Onwrikbaar/NeoDK/Enclosure/blue.png

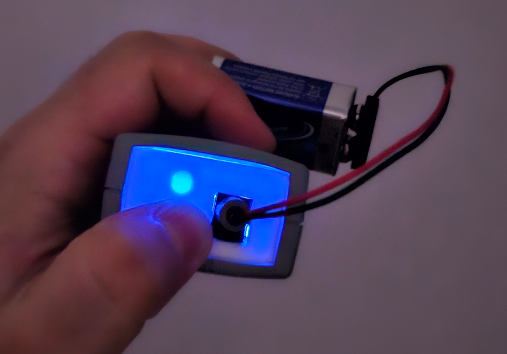
Enclosure/blue.png
