Onwrikbaar/NeoDK/pictures/enclosure.png

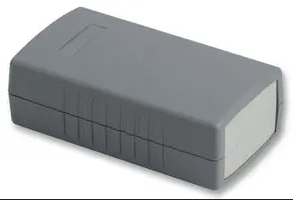
pictures/enclosure.png
