Onwrikbaar/NeoDK/firmware/neodk/src/debug_cli.c

/*
 * debug_cli.c
 *
 *  NOTICE (do not remove):
 *      This file is part of project NeoDK (https://github.com/Onwrikbaar/NeoDK).
 *      See https://github.com/Onwrikbaar/NeoDK/blob/main/LICENSE.txt for full license details.
 *
 *  Created on: 26 Mar 2024
 *      Author: mark
 *   Copyright  2024, 2025 Neostim™
 */

#include <stdio.h>

#include "bsp_dbg.h"
#include "bsp_mao.h"
#include "bsp_app.h"
#include "app_event.h"

// This module implements:
#include "debug_cli.h"


typedef struct {
    uint8_t buf[20];
    EventQueue *delegate;
    Sequencer *sequencer;
    DataLink *datalink;
    uint8_t state;
    uint8_t len;
} CmndInterp;

static CmndInterp my = {0};


static void gatherInputCharacters(CmndInterp *me, char ch)
{
    me->buf[me->len] = '\0';
    if (ch == '\n' || (me->buf[me->len++] = ch, me->len == sizeof me->buf)) {
        if (ch != '\n') BSP_logf("\n");         // Buffer is full, no newline seen.
        BSP_logf("Console: '%s'\n", me->buf);
        me->len = 0;
    }
}


static void setIntensity(CmndInterp *me, uint8_t intensity_perc)
{
    EventQueue_postEvent((EventQueue *)me->sequencer, ET_SET_INTENSITY, &intensity_perc, sizeof intensity_perc);
}


static void changeIntensity(CmndInterp *me, int8_t delta_perc)
{
    int16_t soll_perc = (int16_t)Sequencer_getIntensityPercentage(me->sequencer) + delta_perc;
    if (soll_perc < 10) soll_perc = 10;
    else if (soll_perc > 100) soll_perc = 100;
    setIntensity(me, soll_perc);
}

/**
 * @brief   Console commands for interactive testing.
 */
static void interpretCommand(CmndInterp *me, char ch)
{
    switch (ch)
    {
        case '?':
            CLI_logf("Commands: /? /a /b /d /l /n /q /s /u /v /w /0 /1../9\n");
            break;
        case '0':
            BSP_primaryVoltageEnable(false);
            setIntensity(me, 0);
            break;
        case '1': case '2': case '3': case '4': case '5': case '6': case '7': case '8': case '9':
            setIntensity(me, (ch - '0') * 10);  // 0..90%.
            BSP_primaryVoltageEnable(true);     // Turn on the buck converter.
            break;
        case 'a':
            BSP_triggerADC();
            break;
        case 'b':                               // Simulate a button press.
            EventQueue_postEvent(me->delegate, ET_BUTTON_PUSHED, NULL, 0);
            EventQueue_postEvent(me->delegate, ET_BUTTON_RELEASED, NULL, 0);
            break;
        case 'd':                               // Intensity down.
            changeIntensity(me, -2);
            break;
        case 'l':
            BSP_toggleTheLED();
            break;
        case 'n':
            EventQueue_postEvent((EventQueue *)me->sequencer, ET_SELECT_NEXT_PATTERN, NULL, 0);
            break;
        case 'q': {                             // Quit.
            int sig = 2;                        // Simulate Ctrl-C.
            EventQueue_postEvent(me->delegate, ET_POSIX_SIGNAL, (uint8_t const *)&sig, sizeof sig);
            break;
        }
        case 's':
            EventQueue_postEvent((EventQueue *)me->sequencer, ET_STOP, NULL, 0);
            break;
        case 'u':                               // Intensity up.
            changeIntensity(me, +2);
            break;
        case 'v':
            CLI_logf("Firmware %s\n", BSP_firmwareVersion());
            break;
        case 'w':                               // Allow rediscovery by Dweeb.
            CLI_logf("Accept connection from Dweeb\n");
            DataLink_awaitSync(me->datalink);
            break;
        default:
            CLI_logf("Unknown command '/%c'\n", ch);
    }
}


static void handleConsoleInput(CmndInterp *me, char ch)
{
    if (me->state == 0) {
        if (ch == '/') me->state = 1;
        else gatherInputCharacters(me, ch);
    } else {                                    // '/' seen.
        if (ch == '\n') {                       // Not a command.
            gatherInputCharacters(me, '/');
            gatherInputCharacters(me, ch);
        } else {
            BSP_logf("\n");
            interpretCommand(me, ch);
        }
        me->state = 0;
    }
}


static void vLogToUser(CmndInterp *me, char const *fmt, va_list args)
{
    char msg[80];
    int nbw = vsnprintf(msg, sizeof msg, fmt, args);
    if (nbw > 0) DataLink_sendDebugPacket(me->datalink, (uint8_t const *)msg, nbw + 1);
}

/*
 * Below are the functions implementing this module's interface.
 */

void CLI_init(EventQueue *dq, Sequencer *sequencer, DataLink *datalink)
{
    my.delegate = dq;
    my.sequencer = sequencer;
    my.datalink = datalink;
}


int CLI_logf(char const *fmt, ...)
{
    va_list args;
    va_start(args, fmt);
    int nbw = BSP_vlogf(fmt, args);
    vLogToUser(&my, fmt, args);
    va_end(args);
    return nbw;
}


void CLI_handleRemoteInput(uint8_t const *cmnd, uint16_t len)
{
    if (len == 2 && cmnd[0] == '/') {
        interpretCommand(&my, cmnd[1]);
    } else {
        char response[len + 5];
        int nc = snprintf(response, sizeof response, "'%.*s'?\n", len, cmnd);
        if (nc > 0 && nc < sizeof response) {
            DataLink_sendDebugPacket(my.datalink, (uint8_t const *)response, nc);
        }
    }
}


void BSP_idle(bool (*maySleep)(void const *), void const *context)
{
    char ch;
    if (BSP_readConsole(&ch, 1)) {
        handleConsoleInput(&my, ch);
    }

    if (maySleep != NULL) {
        BSP_criticalSectionEnter();
        if (maySleep(context)) {
            // All pending events have been handled.
            BSP_sleepMCU();
        }
        BSP_criticalSectionExit();
    }
}
