Onwrikbaar/NeoDK/firmware/neodk/src/pattern_iter.c

/*
 * pattern_iter.c
 *
 *  NOTICE (do not remove):
 *      This file is part of project NeoDK (https://github.com/Onwrikbaar/NeoDK).
 *      See https://github.com/Onwrikbaar/NeoDK/blob/main/LICENSE.txt for full license details.
 *
 *  Created on: 6 Mar 2024
 *      Author: mark
 *   Copyright  2024, 2025 Neostim™
 */

#include "bsp_dbg.h"

// This module implements:
#include "pattern_iter.h"


static void nextElconIfLastStep(PatternIterator *me)
{
    PatternDescr const *pd = me->pattern_descr;
    if (me->step_nr == pd->nr_of_steps - 1) {   // Transition done.
        me->step_nr = 0;
        if (++me->elcon_nr == pd->nr_of_elcons) {
            me->elcon_nr = 0;                   // Wrap around.
            me->nr_of_reps -= 1;
        }
    }
}


static uint8_t const *getNextPattern(PatternIterator *me, uint16_t *nr_of_pulses)
{
    PatternDescr const *pd = me->pattern_descr;
    uint8_t elcon_nr = me->elcon_nr;
    if (me->segment_nr == 0) {
        *nr_of_pulses = pd->nr_of_steps - me->step_nr - 1;
        me->segment_nr = 1;
    } else {
        if (++elcon_nr == pd->nr_of_elcons) elcon_nr = 0;
        *nr_of_pulses = ++me->step_nr;
        nextElconIfLastStep(me);
        me->segment_nr = 0;
    }
    return pd->pattern[elcon_nr];
}


static bool getNextBurst(PatternIterator *me, Burst *burst)
{
    if (PatternIterator_done(me)) return false;

    uint8_t const *elcon = getNextPattern(me, &burst->nr_of_pulses);
    burst->elcon[0] = elcon[0];
    burst->elcon[1] = elcon[1];
    burst->pulse_width_¼µs = me->pulse_width_micros * 4;
    burst->pace_µs = me->pattern_descr->pace_µs;
    return true;
}


static uint8_t getPhase(uint8_t const elcon[2])
{
    M_ASSERT((elcon[0] & elcon[1]) == 0);       // Prevent shorts.
    return (elcon[0] & 0x5) ? 0 : 1;
}


static bool startBurst(Burst const *burst)
{
    if (Burst_isValid(burst)) {
        BSP_setElectrodeConfiguration(burst->elcon);
        return BSP_startBurst(burst);
    }

    BSP_logf("Invalid burst\n   ");
    Burst_print(burst);
    return false;
}

/*
 * Below are the functions implementing this module's interface.
 */

bool PatternIterator_init(PatternIterator *me, PatternDescr const *pd)
{
    me->pattern_descr = pd;
    me->amplitude = 0;
    me->nr_of_reps = pd->nr_of_reps;
    me->elcon_nr = 0;
    me->step_nr = 0;
    me->segment_nr = 0;                         // 0 or 1.
    return pd->nr_of_steps != 0;
}


void PatternIterator_setPulseWidth(PatternIterator *me, uint8_t width_µs)
{
    BSP_logf("Setting pulse width to %hhu µs\n", width_µs);
    me->pulse_width_micros = width_µs;
}


bool PatternIterator_scheduleNextBurst(PatternIterator *me)
{
    Burst burst;
    if (getNextBurst(me, &burst)) {
        if (burst.pulse_width_¼µs > MAX_PULSE_WIDTH_¼µs) {
            burst.pulse_width_¼µs = MAX_PULSE_WIDTH_¼µs;
        }
        // BSP_logf("Pulse width is %hu µs\n", Burst_pulseWidth_µs(&burst));
        burst.phase = getPhase(burst.elcon);
        // TODO Set burst.amplitude?
        return startBurst(&burst);
    }

    return false;
}


char const *PatternIterator_name(PatternIterator const *me)
{
    return Patterns_name(me->pattern_descr);
}


bool PatternIterator_done(PatternIterator *me)
{
    return me->nr_of_reps == 0;
}
