Onwrikbaar/NeoDK/firmware/neodk/inc/bsp_app.h

/*
 * bsp_app.h -- The application's Board Support Package interface.
 *
 *  NOTICE (do not remove):
 *      This file is part of project NeoDK (https://github.com/Onwrikbaar/NeoDK).
 *      See https://github.com/Onwrikbaar/NeoDK/blob/main/LICENSE.txt for full license details.
 *
 *  Created on: 6 Oct 2020
 *      Author: mark
 *   Copyright  2020..2026 Neostim™
 */

#ifndef INC_BSP_APP_H_
#define INC_BSP_APP_H_

#include "convenience.h"
#include "eventqueue.h"
#include "burst.h"

typedef struct {
    uint16_t Vbat_mV, Vcap_mV, Iprim_mA;
} AdcValues;


void BSP_init(void);                            // Get the hardware ready for action.
void BSP_registerPulseDelegate(EventQueue *);
void BSP_toggleTheLED(void);
uint32_t BSP_millisecondsToTicks(uint16_t ms);
uint64_t BSP_ticksToMicroseconds(uint64_t ticks);
uint64_t BSP_microsecondsSinceBoot(void);

// To install some handlers.
void BSP_registerIdleHandler(Selector *);
void BSP_registerButtonHandler(Selector *);

// Pulse generation related functions.
uint16_t BSP_setPrimaryVoltagePercent(uint8_t perc);
void BSP_primaryVoltageEnable(bool must_be_on);
void BSP_setElectrodeConfiguration(uint8_t const [2]);
void BSP_startSequencerClock(uint32_t time_µs);
void BSP_stopSequencerClock(void);
void BSP_resumeSequencerClock(void);
bool BSP_scheduleBurst(Burst const *);
bool BSP_startBurst(Burst const *);

// Debugging stuff.
void BSP_triggerADC(void);

// Firmware update.
uint32_t const *BSP_serialNumber(void);
char const *BSP_firmwareVersion();
char const *BSP_deviceTypeName();
void BSP_gotoDfuMode(void);

// Close any communication ports and release resources, if applicable.
void BSP_close(void);
void BSP_sleepMCU(void);
void BSP_shutDown(void);

#endif
