Onwrikbaar/NeoDK/firmware/neodk/inc/app_event.h

/*
 * app_event.h -- the application event types
 *  Note: keep any and all platform dependencies out of this file.
 * 
 *  NOTICE (do not remove):
 *      This file is part of project NeoDK (https://github.com/Onwrikbaar/NeoDK).
 *      See https://github.com/Onwrikbaar/NeoDK/blob/main/LICENSE.txt for full license details.
 *
 *  Created on: 22 May 2021
 *      Author: Mark
 *   Copyright  2021..2025 Neostim™
 */

#ifndef INC_APP_EVENT_H_
#define INC_APP_EVENT_H_

#include "ao_event.h"

// Make sure the ordinals are >= ET_FIRST_APP_EVENT.
enum {
    ET_THIRD_PARTY = ET_AO_FIRST_APP_EVENT,     // To keep other libs working.
    ET_APP_HEARTBEAT, ET_ADC_DATA_AVAILABLE,
    ET_DEBUG_SYNC, ET_DATAGRAM_SYNC, ET_INCOMING_PACKET,
    // ET_CONTROLLER_CONNECTED, ET_CONTROLLER_DISCONNECTED,
    ET_PLAY, ET_PAUSE, ET_STOP, ET_UNKNOWN_COMMAND, ET_TOGGLE_PLAY_PAUSE,
    ET_SELECT_NEXT_PATTERN, ET_SELECT_PATTERN_BY_NAME, ET_SET_INTENSITY,
    ET_QUEUE_PULSE_TRAIN, ET_START_STREAM, ET_STOP_STREAM,
    ET_BAD_BURST, ET_BURST_STARTED, ET_BURST_COMPLETED, ET_BURST_EXPIRED,
};

#endif
