Onwrikbaar/NeoDK/firmware/neodk/inc/attributes.h

/*
 * attributes.h
 *
 *  NOTICE (do not remove):
 *      This file is part of project NeoDK (https://github.com/Onwrikbaar/NeoDK).
 *      See https://github.com/Onwrikbaar/NeoDK/blob/main/LICENSE.txt for full license details.
 *
 *  Created on: 15 Oct 2024
 *      Author: mark
 *   Copyright  2024, 2025 Neostim™
 */

#ifndef INC_ATTRIBUTES_H_
#define INC_ATTRIBUTES_H_

#include "matter.h"

typedef enum {
    AI_FIRMWARE_VERSION = 2, AI_VOLTAGES, AI_CLOCK_MICROS,
    AI_ALL_PATTERN_NAMES, AI_CURRENT_PATTERN_NAME, AI_INTENSITY_PERCENT, AI_PLAY_PAUSE_STOP,
    AI_BOX_NAME, AI_PT_DESCRIPTOR_QUEUE, AI_HEARTBEAT_INTERVAL_SECS
} AttributeId;

typedef void (*AttrNotifier)(void *target, AttributeId, TransactionId, ElementEncoding, uint8_t const *data, uint16_t size);

#define NO_TRANS_ID     (TransactionId)0U

#ifdef __cplusplus
extern "C" {
#endif

SubscriptionId Attribute_awaitRead(AttributeId, TransactionId, AttrNotifier, void *target);
SubscriptionId Attribute_subscribe(AttributeId, TransactionId, AttrNotifier, void *target);
void Attribute_changed(AttributeId, TransactionId, ElementEncoding, uint8_t const *data, uint16_t size);

#ifdef __cplusplus
}
#endif

#endif
